robegamesios/PlexMatrixDisplay/PlexMatrixDisplay/src/weatherIcons.h

#ifdef WEATHERCLOCK_MODE

#include <stdint.h>

static uint32_t sun_24x24[] PROGMEM  = {
  0x000000, 0x000000, 0x000000, 0x000000, 0x000000, 0x000000, 0x000000, 0x000000, 0xffe177, 0xffe177, 0xffff80, 0x000000, 0x000000, 0xffff80, 0xffe177, 0xffe177, 0x000000, 0x000000, 0x000000, 0x000000, 0x000000, 0x000000, 0x000000, 0x000000, 
  0x000000, 0x000000, 0x000000, 0x000000, 0x000000, 0x000000, 0x000000, 0xffff00, 0xffe177, 0xffe177, 0xffe177, 0xffe376, 0xffe379, 0xffe177, 0xffe177, 0xffe177, 0xffff00, 0x000000, 0x000000, 0x000000, 0x000000, 0x000000, 0x000000, 0x000000, 
  0x000000, 0x000000, 0x000000, 0x000000, 0x000000, 0x000000, 0x000000, 0xffe278, 0xffe177, 0xffe177, 0xffe177, 0xffe177, 0xffe177, 0xffe177, 0xffe177, 0xffe177, 0xffe177, 0x000000, 0x000000, 0x000000, 0x000000, 0x000000, 0x000000, 0x000000, 
  0x000000, 0x000000, 0x000000, 0xffe177, 0xffe277, 0xffe177, 0xffe277, 0xffe177, 0xffe177, 0xffe177, 0xffe177, 0xffdf73, 0xffdf73, 0xffe177, 0xffe177, 0xffe177, 0xffe177, 0xffe277, 0xffd767, 0xffd35d, 0xffd25d, 0x000000, 0x000000, 0x000000, 
  0x000000, 0x000000, 0x000000, 0xffe077, 0xffe177, 0xffe177, 0xffe177, 0xffe177, 0xffd767, 0xffcc53, 0xffc446, 0xffc344, 0xffc344, 0xffc446, 0xffcc53, 0xffd868, 0xffe177, 0xffe177, 0xffdb6c, 0xffd15b, 0xffd35d, 0x000000, 0x000000, 0x000000, 
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
  0x000000, 0x000000, 0x000000, 0x000000, 0x000000, 0x000000, 0x000000, 0x000000, 0x000000, 0x000000, 0x000000, 0x000000, 0x000000, 0x000000, 0x000000, 0x000000, 0x000000, 0x000000, 0x000000, 0x000000, 0x000000, 0x000000, 0x000000, 0x000000, 
  0x000000, 0x000000, 0x000000, 0x000000, 0x000000, 0x000000, 0x000000, 0x000000, 0x000000, 0x000000, 0x000000, 0x000000, 0x000000, 0x000000, 0x000000, 0x000000, 0x000000, 0x000000, 0x000000, 0x000000, 0x000000, 0x000000, 0x000000, 0x000000
};

#endif
